Javis79/Chess-learning-system/Grafiki/agh_znk-removebg-preview.png

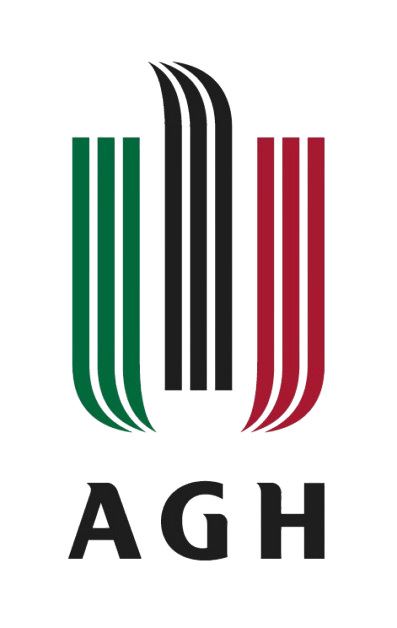
Grafiki/agh_znk-removebg-preview.png
