Javis79/Chess-learning-system/Grafiki/Wizualizacja.png

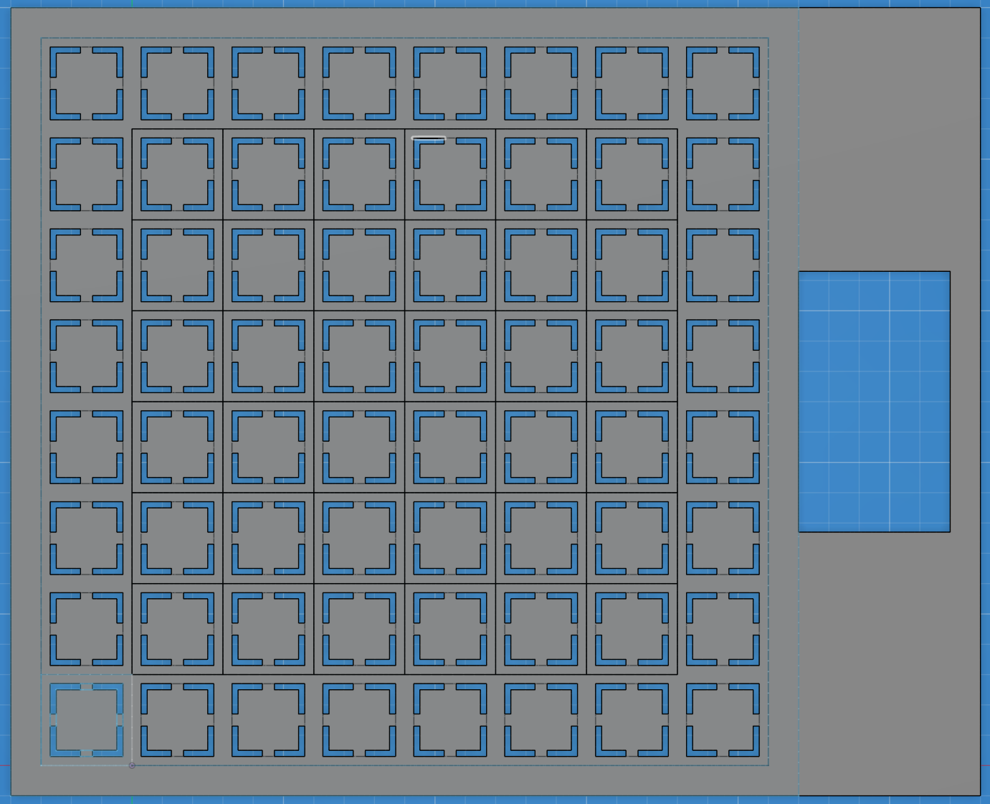
Grafiki/Wizualizacja.png
