Javis79/Chess-learning-system/PCB_inzynierka/screens/Screenshot from 2025-11-08 16-29-01.png

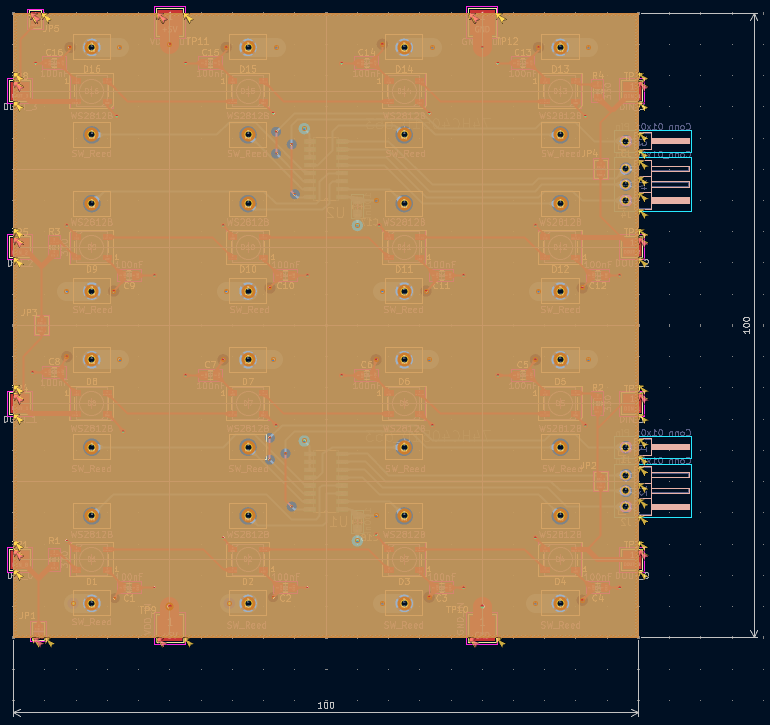
PCB_inzynierka/screens/Screenshot from 2025-11-08 16-29-01.png
