Javis79/Chess-learning-system/test_both/test_both.ioc

Mcu.UserName=STM32F401RETx
PA0-WKUP.Signal=GPIO_Input
PA1.Signal=GPIO_Input
PA13.GPIO_Label=TMS
PA13.Signal=SYS_JTMS-SWDIO
PA14.GPIO_Label=TCK
PA14.Signal=SYS_JTCK-SWCLK
PA2.GPIO_Label=USART_TX
PA2.Signal=USART2_TX
PA3.GPIO_Label=USART_RX
PA3.Signal=USART2_RX
PA4.Signal=GPIO_Input
PA5.Signal=SPI1_SCK
PA6.Signal=SPI1_MISO
PA7.Signal=SPI1_MOSI
PA8.Signal=S_TIM1_CH1
PA9.Signal=GPIO_Output
PB0.Signal=GPIO_Output
PB10.Signal=SPI2_SCK
PB3.GPIO_Label=SWO
PB3.Signal=SYS_JTDO-SWO
PB6.Signal=GPIO_Output
PC0.Signal=GPIO_Output
PC1.Signal=GPIO_Output
PC13-ANTI_TAMP.GPIO_Label=B1 [Blue PushButton]
PC13-ANTI_TAMP.Signal=GPXTI13
PC14-OSC32_IN.Signal=RCC_OSC32_IN
PC15-OSC32_OUT.Signal=RCC_OSC32_OUT
PC2.Signal=SPI2_MISO
PC3.Signal=SPI2_MOSI
PC4.Signal=GPIO_Input
PC7.Signal=GPIO_Output
