Javis79/Chess-learning-system/test_both/Core/Inc/main.h

#define LCD_CS_GPIO_Port   GPIOC
#define LCD_CS_Pin         GPIO_PIN_7
#define LCD_DC_GPIO_Port   GPIOA
#define LCD_DC_Pin         GPIO_PIN_9
#define LCD_RST_GPIO_Port  GPIOB
#define LCD_RST_Pin        GPIO_PIN_6
#define B1_Pin GPIO_PIN_13
#define B1_GPIO_Port GPIOC
#define USART_TX_Pin GPIO_PIN_2
#define USART_TX_GPIO_Port GPIOA
#define USART_RX_Pin GPIO_PIN_3
#define USART_RX_GPIO_Port GPIOA
#define TMS_Pin GPIO_PIN_13
#define TMS_GPIO_Port GPIOA
#define TCK_Pin GPIO_PIN_14
#define TCK_GPIO_Port GPIOA
#define SWO_Pin GPIO_PIN_3
#define SWO_GPIO_Port GPIOB
#define SD_SPI_HANDLE hspi1
