Javis79/Chess-learning-system/test_both/Core/Src/spi.c

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
/* Includes ------------------------------------------------------------------*/
#include "spi.h"

#define CS_TFT_GPIO_Port   GPIOB
#define CS_TFT_Pin         GPIO_PIN_6
#define DC_TFT_GPIO_Port   GPIOA
#define DC_TFT_Pin         GPIO_PIN_9
#define RST_TFT_GPIO_Port  GPIOC
#define RST_TFT_Pin        GPIO_PIN_7
#define CS_SD_GPIO_Port    GPIOA
#define CS_SD_Pin          GPIO_PIN_10

SPI_HandleTypeDef hspi1;
DMA_HandleTypeDef hdma_spi1_tx;

SPI_HandleTypeDef hspi2;
DMA_HandleTypeDef hdma_spi2_tx;

/* SPI1 init function */
void MX_SPI1_Init(void)
{

  hspi1.Instance = SPI1;
  hspi1.Init.Mode = SPI_MODE_MASTER;
  hspi1.Init.Direction = SPI_DIRECTION_2LINES;
  hspi1.Init.DataSize = SPI_DATASIZE_8BIT;
  hspi1.Init.CLKPolarity = SPI_POLARITY_LOW;
  hspi1.Init.CLKPhase = SPI_PHASE_1EDGE;
  hspi1.Init.NSS = SPI_NSS_SOFT;
  hspi1.Init.BaudRatePrescaler = SPI_BAUDRATEPRESCALER_8;
  hspi1.Init.FirstBit = SPI_FIRSTBIT_MSB;
  hspi1.Init.TIMode = SPI_TIMODE_DISABLE;
  hspi1.Init.CRCCalculation = SPI_CRCCALCULATION_DISABLE;
  hspi1.Init.CRCPolynomial = 10;
  if (HAL_SPI_Init(&hspi1) != HAL_OK)
  {
    Error_Handler();
  }
}

void MX_SPI2_Init(void)
{

  hspi2.Instance = SPI2;
  hspi2.Init.Mode = SPI_MODE_MASTER;
  hspi2.Init.Direction = SPI_DIRECTION_2LINES;
  hspi2.Init.DataSize = SPI_DATASIZE_8BIT;
  hspi2.Init.CLKPolarity = SPI_POLARITY_LOW;
  hspi2.Init.CLKPhase = SPI_PHASE_1EDGE;
  hspi2.Init.NSS = SPI_NSS_SOFT;
  hspi2.Init.BaudRatePrescaler = SPI_BAUDRATEPRESCALER_256;
  hspi2.Init.FirstBit = SPI_FIRSTBIT_MSB;
  hspi2.Init.TIMode = SPI_TIMODE_DISABLE;
  hspi2.Init.CRCCalculation = SPI_CRCCALCULATION_DISABLE;
  hspi2.Init.CRCPolynomial = 10;
  if (HAL_SPI_Init(&hspi2) != HAL_OK)
  {
    Error_Handler();
  }
}


void HAL_SPI_MspInit(SPI_HandleTypeDef* spiHandle)
{

  GPIO_InitTypeDef GPIO_InitStruct = {0};
  if(spiHandle->Instance==SPI1)
  {
    /* SPI1 clock enable */
    __HAL_RCC_SPI1_CLK_ENABLE();

    __HAL_RCC_GPIOA_CLK_ENABLE();
    /**SPI1 GPIO Configuration
    PA5     ------> SPI1_SCK
    PA6     ------> SPI1_MISO
    PA7     ------> SPI1_MOSI
    */
    GPIO_InitStruct.Pin = GPIO_PIN_5|GPIO_PIN_6|GPIO_PIN_7;
    GPIO_InitStruct.Mode = GPIO_MODE_AF_PP;
    GPIO_InitStruct.Pull = GPIO_NOPULL;
    GPIO_InitStruct.Speed = GPIO_SPEED_FREQ_VERY_HIGH;
    GPIO_InitStruct.Alternate = GPIO_AF5_SPI1;
    HAL_GPIO_Init(GPIOA, &GPIO_InitStruct);

    /* SPI1 DMA Init */
    /* SPI1_TX Init */
    hdma_spi1_tx.Instance = DMA2_Stream3;
    hdma_spi1_tx.Init.Channel = DMA_CHANNEL_3;
    hdma_spi1_tx.Init.Direction = DMA_MEMORY_TO_PERIPH;
    hdma_spi1_tx.Init.PeriphInc = DMA_PINC_DISABLE;
    hdma_spi1_tx.Init.MemInc = DMA_MINC_ENABLE;
    hdma_spi1_tx.Init.PeriphDataAlignment = DMA_PDATAALIGN_BYTE;
    hdma_spi1_tx.Init.MemDataAlignment = DMA_MDATAALIGN_BYTE;
    hdma_spi1_tx.Init.Mode = DMA_NORMAL;
    hdma_spi1_tx.Init.Priority = DMA_PRIORITY_LOW;
    hdma_spi1_tx.Init.FIFOMode = DMA_FIFOMODE_DISABLE;
    if (HAL_DMA_Init(&hdma_spi1_tx) != HAL_OK)
    {
      Error_Handler();
    }

    __HAL_LINKDMA(spiHandle,hdmatx,hdma_spi1_tx);

  }

  if(spiHandle->Instance==SPI2)
   {
     /* SPI2 clock enable */
     __HAL_RCC_SPI2_CLK_ENABLE();

     __HAL_RCC_GPIOC_CLK_ENABLE();
     __HAL_RCC_GPIOB_CLK_ENABLE();
     /**SPI2 GPIO Configuration
     PC2     ------> SPI2_MISO
     PC3     ------> SPI2_MOSI
     PB10     ------> SPI2_SCK
     */
     GPIO_InitStruct.Pin = GPIO_PIN_2|GPIO_PIN_3;
     GPIO_InitStruct.Mode = GPIO_MODE_AF_PP;
     GPIO_InitStruct.Pull = GPIO_NOPULL;
     GPIO_InitStruct.Speed = GPIO_SPEED_FREQ_VERY_HIGH;
     GPIO_InitStruct.Alternate = GPIO_AF5_SPI2;
     HAL_GPIO_Init(GPIOC, &GPIO_InitStruct);

     GPIO_InitStruct.Pin = GPIO_PIN_10;
     GPIO_InitStruct.Mode = GPIO_MODE_AF_PP;
     GPIO_InitStruct.Pull = GPIO_NOPULL;
     GPIO_InitStruct.Speed = GPIO_SPEED_FREQ_VERY_HIGH;
     GPIO_InitStruct.Alternate = GPIO_AF5_SPI2;
     HAL_GPIO_Init(GPIOB, &GPIO_InitStruct);

     /* SPI2 DMA Init */
     /* SPI2_TX Init */
     hdma_spi2_tx.Instance = DMA1_Stream4;
     hdma_spi2_tx.Init.Channel = DMA_CHANNEL_0;
     hdma_spi2_tx.Init.Direction = DMA_MEMORY_TO_PERIPH;
     hdma_spi2_tx.Init.PeriphInc = DMA_PINC_DISABLE;
     hdma_spi2_tx.Init.MemInc = DMA_MINC_ENABLE;
     hdma_spi2_tx.Init.PeriphDataAlignment = DMA_PDATAALIGN_BYTE;
     hdma_spi2_tx.Init.MemDataAlignment = DMA_MDATAALIGN_BYTE;
     hdma_spi2_tx.Init.Mode = DMA_NORMAL;
     hdma_spi2_tx.Init.Priority = DMA_PRIORITY_LOW;
     hdma_spi2_tx.Init.FIFOMode = DMA_FIFOMODE_DISABLE;
     if (HAL_DMA_Init(&hdma_spi2_tx) != HAL_OK)
     {
       Error_Handler();
     }

     __HAL_LINKDMA(spiHandle,hdmatx,hdma_spi2_tx);

   }

}

void HAL_SPI_MspDeInit(SPI_HandleTypeDef* spiHandle)
{

  if(spiHandle->Instance==SPI1)
  {
    /* Peripheral clock disable */
    __HAL_RCC_SPI1_CLK_DISABLE();

    /**SPI1 GPIO Configuration
    PA5     ------> SPI1_SCK
    PA6     ------> SPI1_MISO
    PA7     ------> SPI1_MOSI
    */
    HAL_GPIO_DeInit(GPIOA, GPIO_PIN_5|GPIO_PIN_6|GPIO_PIN_7);

    /* SPI1 DMA DeInit */
    HAL_DMA_DeInit(spiHandle->hdmatx);
  }

  if(spiHandle->Instance==SPI2)
    {
      /* Peripheral clock disable */
      __HAL_RCC_SPI2_CLK_DISABLE();

      /**SPI2 GPIO Configuration
      PC2     ------> SPI2_MISO
      PC3     ------> SPI2_MOSI
      PB10     ------> SPI2_SCK
      */
      HAL_GPIO_DeInit(GPIOC, GPIO_PIN_2|GPIO_PIN_3);

      HAL_GPIO_DeInit(GPIOB, GPIO_PIN_10);

      /* SPI2 DMA DeInit */
      HAL_DMA_DeInit(spiHandle->hdmatx);
    }

}
