Javis79/Chess-learning-system/test_both/Core/Src/gpio.c

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

/* Includes ------------------------------------------------------------------*/
#include "gpio.h"

/*----------------------------------------------------------------------------*/
/* Configure GPIO                                                             */
/*----------------------------------------------------------------------------*/
/** Configure pins as
        * Analog
        * Input
        * Output
        * EVENT_OUT
        * EXTI
*/
void MX_GPIO_Init(void)
{

	GPIO_InitTypeDef GPIO_InitStruct = {0};

	/* GPIO Ports Clock Enable */
	__HAL_RCC_GPIOC_CLK_ENABLE();
	__HAL_RCC_GPIOH_CLK_ENABLE();
	__HAL_RCC_GPIOA_CLK_ENABLE();
	__HAL_RCC_GPIOB_CLK_ENABLE();


	//SCREEN RESET
	HAL_GPIO_WritePin(GPIOC, GPIO_PIN_7, GPIO_PIN_RESET);
	//SCREEN DC
	HAL_GPIO_WritePin(GPIOA, GPIO_PIN_9, GPIO_PIN_RESET);
	//SCREEN CS
	HAL_GPIO_WritePin(GPIOB, GPIO_PIN_6, GPIO_PIN_RESET);

	/*Configure GPIO pin : B1_Pin */
	GPIO_InitStruct.Pin = B1_Pin;
	GPIO_InitStruct.Mode = GPIO_MODE_IT_FALLING;
	GPIO_InitStruct.Pull = GPIO_NOPULL;
	HAL_GPIO_Init(B1_GPIO_Port, &GPIO_InitStruct);

	/*Configure GPIO pin : PC7 */
	GPIO_InitStruct.Pin = GPIO_PIN_7;
	GPIO_InitStruct.Mode = GPIO_MODE_OUTPUT_PP;
	GPIO_InitStruct.Pull = GPIO_NOPULL;
	GPIO_InitStruct.Speed = GPIO_SPEED_FREQ_LOW;
	HAL_GPIO_Init(GPIOC, &GPIO_InitStruct);

	/*Configure GPIO pin : PA9 */
	GPIO_InitStruct.Pin = GPIO_PIN_9;
	GPIO_InitStruct.Mode = GPIO_MODE_OUTPUT_PP;
	GPIO_InitStruct.Pull = GPIO_NOPULL;
	GPIO_InitStruct.Speed = GPIO_SPEED_FREQ_LOW;
	HAL_GPIO_Init(GPIOA, &GPIO_InitStruct);

	/*Configure GPIO pin : PB6 */
	GPIO_InitStruct.Pin = GPIO_PIN_6;
	GPIO_InitStruct.Mode = GPIO_MODE_OUTPUT_PP;
	GPIO_InitStruct.Pull = GPIO_NOPULL;
	GPIO_InitStruct.Speed = GPIO_SPEED_FREQ_LOW;
	HAL_GPIO_Init(GPIOB, &GPIO_InitStruct);

	HAL_GPIO_WritePin(GPIOC, GPIO_PIN_0|GPIO_PIN_1, GPIO_PIN_RESET);

	/*Configure GPIO pin Output Level */
	HAL_GPIO_WritePin(GPIOB, GPIO_PIN_0, GPIO_PIN_RESET);

	/* Configure GPIO pins : PC0 PC1 as inputs (mux outputs) */
	GPIO_InitStruct.Pin = GPIO_PIN_0 | GPIO_PIN_1;
	GPIO_InitStruct.Mode = GPIO_MODE_INPUT;
	GPIO_InitStruct.Pull = GPIO_PULLDOWN;
	HAL_GPIO_Init(GPIOC, &GPIO_InitStruct);


	// BUTTONS
	// Konfiguracja pinów PA0, PA1, PA4, PB0 jako wejścia z wewnętrznymi rezystorami pull-up
	GPIO_InitStruct.Pin = GPIO_PIN_0 | GPIO_PIN_1 | GPIO_PIN_4;  // PA0, PA1, PA4
	GPIO_InitStruct.Mode = GPIO_MODE_INPUT;
	GPIO_InitStruct.Pull = GPIO_PULLUP;  // Pull-up
	HAL_GPIO_Init(GPIOA, &GPIO_InitStruct);
	GPIO_InitStruct.Pin = GPIO_PIN_0;  // PB0
	GPIO_InitStruct.Pull = GPIO_PULLUP;  // Pull-up
	HAL_GPIO_Init(GPIOB, &GPIO_InitStruct);

	//MUX SELECT PINS
	GPIO_InitStruct.Pin = GPIO_PIN_10 | GPIO_PIN_11 | GPIO_PIN_12; // PC10, PC11, PC12
	GPIO_InitStruct.Mode = GPIO_MODE_OUTPUT_PP;  // Tryb wyjścia push-pull
	GPIO_InitStruct.Pull = GPIO_NOPULL;          // Bez rezystorów pull-up/pull-down
	GPIO_InitStruct.Speed = GPIO_SPEED_FREQ_LOW; // Niska prędkość
	HAL_GPIO_Init(GPIOC, &GPIO_InitStruct);

	//SD CARD CS
	GPIO_InitStruct.Pin = GPIO_PIN_10;
	GPIO_InitStruct.Mode = GPIO_MODE_OUTPUT_PP;
	GPIO_InitStruct.Pull = GPIO_PULLUP;
	GPIO_InitStruct.Speed = GPIO_SPEED_FREQ_LOW;
	HAL_GPIO_Init(GPIOA, &GPIO_InitStruct);



}
