Javis79/Chess-learning-system/test_both/Core/Inc/buttons.h

/*
 * buttons.h
 *
 *  Created on: Oct 16, 2025
 *      Author: javis
 */


#ifndef INC_BUTTONS_H_
#define INC_BUTTONS_H_

#include "gpio.h"
#include "stdint.h"

int button1_pressed(void);
int button2_pressed(void);
int button3_pressed(void);
int button4_pressed(void);


#endif /* INC_BUTTONS_H_ */
