Javis79/Chess-learning-system/test_both/Core/Inc/lcd_scheduler.h

/*
 * lcd_scheduler.h
 *
 *  Created on: Sep 30, 2025
 *      Author: javis
 */

#pragma once
#ifndef INC_LCD_SCHEDULER_H_
#define INC_LCD_SCHEDULER_H_

void lcd_scheduler_init(void);
void lcd_scheduler_tick(void);

#endif /* INC_LCD_SCHEDULER_H_ */
