Javis79/Chess-learning-system/test_both/Core/Inc/led_scheduler.h

/*
 * led_scheduler.h
 *
 *  Created on: Sep 30, 2025
 *      Author: javis
 */
#pragma once
#ifndef INC_LED_SCHEDULER_H_
#define INC_LED_SCHEDULER_H_

void led_scheduler_init(void);
void led_scheduler_tick(void);


#endif /* INC_LED_SCHEDULER_H_ */
